warezak/PoundNineNewsWire/3DModel/Solidworks files/93365A11021-08-2015.SLDPRT

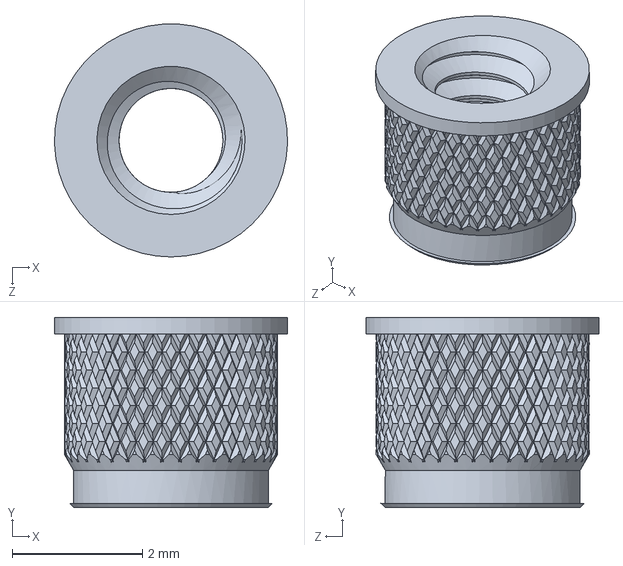
[picture p17: CAD file, 2016-02-17]
3DModel/Solidworks files/93365A11021-08-2015.SLDPRT
3.58 x 2.92 x 3.58 mm
