warezak/PoundNineNewsWire/XMegaFirmware/ATXMEGA_BASECODE/src/config/conf_sysfont.h

/**
 * \file
 *
 * \brief Default configurations for sysfont
 *
 * Copyright (c) 2012 Atmel Corporation. All rights reserved.
 *
 * \asf_license_start
 *
 * \page License
 *
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
 * 3. The name of Atmel may not be used to endorse or promote products derived
 *    from this software without specific prior written permission.
 *
 * 4. This software may only be redistributed and used in connection with an
 *    Atmel microcontroller product.
 *
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
 * \asf_license_stop
 *
 https://bitbucket.org/bperrybap/openglcd/src/86a2ff50f5da42badd289f6012b9200e9b2147bc/fonts/?at=master
 
 */
#ifndef CONF_SYSFONT_H
#define CONF_SYSFONT_H

/**
 * \weakgroup gfx_sysfont
 * @{
 */

#include <stdint.h>

 #define USE_FONT_BPMONO_10x16  // big font
/* #define USE_FONT_BPMONO_10x14 */
/* #define USE_FONT_MONO_MMM_10x12 */
#define USE_FONT_BASIC_6x7  // normal sys font


//#if defined(USE_FONT_BPMONO_10x16)
/** Width of each glyph, including spacer column. */
#  define BIGFONT_WIDTH           10
/** Height of each glyph, excluding spacer line. */
#  define BIGFONT_HEIGHT          16
/** Line height. */
#  define BIGFONT_LINESPACING     8
/** First character defined. */
#  define BIGFONT_FIRSTCHAR       ((uint8_t)' ')
/** Last character defined. */
#  define BIGFONT_LASTCHAR        ((uint8_t)'}')

/** Define variable containing the font */
#  define BIGFONT_DEFINE_GLYPHS \
        /* Glyph data, row by row, MSB is leftmost pixel, one byte per row. */ \
	static PROGMEM_DECLARE(uint8_t, bigfont_glyphs[]) = { \
		/* "BPmono" font (http://www.backpacker.gr) at size 10x16 */ \
		0x00, 0x00, 0x00, 0x00, 0x00, 0x00, 0x00, 0x00, 0x00, 0x00, \
		0x00, 0x00, 0x00, 0x00, 0x00, 0x00, 0x00, 0x00, 0x00, 0x00, \
		0x00, 0x00, 0x00, 0x00, 0x00, 0x00, 0x00, 0x00, 0x00, 0x00, \
		0x00, 0x00, /*   */ \
		0x00, 0x00, 0x00, 0x00, 0x00, 0x00, 0x30, 0x00, 0x30, 0x00, \
		0x30, 0x00, 0x30, 0x00, 0x30, 0x00, 0x30, 0x00, 0x30, 0x00, \
		0x00, 0x00, 0x30, 0x00, 0x30, 0x00, 0x00, 0x00, 0x00, 0x00, \
		0x00, 0x00, /* ! */ \
		0x00, 0x00, 0x00, 0x00, 0x00, 0x00, 0x6C, 0x00, 0x6C, 0x00, \
		0x6C, 0x00, 0x6C, 0x00, 0x00, 0x00, 0x00, 0x00, 0x00, 0x00, \
		0x00, 0x00, 0x00, 0x00, 0x00, 0x00, 0x00, 0x00, 0x00, 0x00, \
		0x00, 0x00, /* " */ \
		0x00, 0x00, 0x00, 0x00, 0x00, 0x00, 0x00, 0x00, 0x48, 0x00, \
		0x48, 0x00, 0xFC, 0x00, 0x48, 0x00, 0x48, 0x00, 0x48, 0x00, \
		0xFC, 0x00, 0x48, 0x00, 0x48, 0x00, 0x00, 0x00, 0x00, 0x00, \
		0x00, 0x00, /* # */ \
		0x00, 0x00, 0x00, 0x00, 0x00, 0x00, 0x10, 0x00, 0x10, 0x00, \
		0x3C, 0x00, 0x40, 0x00, 0x30, 0x00, 0x08, 0x00, 0x04, 0x00, \
		0x78, 0x00, 0x10, 0x00, 0x10, 0x00, 0x00, 0x00, 0x00, 0x00, \
		0x00, 0x00, /* $ */ \
		0x00, 0x00, 0x00, 0x00, 0x00, 0x00, 0x00, 0x00, 0x7C, 0x00, \
		0xA4, 0x00, 0xA8, 0x00, 0x48, 0x00, 0x10, 0x00, 0x14, 0x00, \
		0x2A, 0x00, 0x4A, 0x00, 0x44, 0x00, 0x00, 0x00, 0x00, 0x00, \
		0x00, 0x00, /* % */ \
		0x00, 0x00, 0x00, 0x00, 0x00, 0x00, 0x70, 0x00, 0x88, 0x00, \
		0x88, 0x00, 0x88, 0x00, 0x70, 0x00, 0x88, 0x00, 0x8A, 0x00, \
		0x8A, 0x00, 0x8C, 0x00, 0x70, 0x00, 0x00, 0x00, 0x00, 0x00, \
		0x00, 0x00, /* & */ \
		0x00, 0x00, 0x00, 0x00, 0x00, 0x00, 0x10, 0x00, 0x10, 0x00, \
		0x10, 0x00, 0x00, 0x00, 0x00, 0x00, 0x00, 0x00, 0x00, 0x00, \
		0x00, 0x00, 0x00, 0x00, 0x00, 0x00, 0x00, 0x00, 0x00, 0x00, \
		0x00, 0x00, /* ' */ \
		0x00, 0x00, 0x00, 0x00, 0x08, 0x00, 0x10, 0x00, 0x10, 0x00, \
		0x20, 0x00, 0x20, 0x00, 0x20, 0x00, 0x20, 0x00, 0x20, 0x00, \
		0x20, 0x00, 0x10, 0x00, 0x10, 0x00, 0x08, 0x00, 0x00, 0x00, \
		0x00, 0x00, /* ( */ \
		0x00, 0x00, 0x00, 0x00, 0x20, 0x00, 0x10, 0x00, 0x10, 0x00, \
		0x08, 0x00, 0x08, 0x00, 0x08, 0x00, 0x08, 0x00, 0x08, 0x00, \
		0x08, 0x00, 0x10, 0x00, 0x10, 0x00, 0x20, 0x00, 0x00, 0x00, \
		0x00, 0x00, /* ) */ \
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
	};

#if defined(USE_FONT_BPMONO_10x14)
/** Width of each glyph, including spacer column. */
#  define SYSFONT_WIDTH           10
/** Height of each glyph, excluding spacer line. */
#  define SYSFONT_HEIGHT          14
/** Line height. */
#  define SYSFONT_LINESPACING     8
/** First character defined. */
#  define SYSFONT_FIRSTCHAR       ((uint8_t)' ')
/** Last character defined. */
#  define SYSFONT_LASTCHAR        ((uint8_t)'}')

/** Define variable containing the font */
#  define SYSFONT_DEFINE_GLYPHS \
        /* Glyph data, row by row, MSB is leftmost pixel, one byte per row. */ \
	static PROGMEM_DECLARE(uint8_t, sysfont_glyphs[]) = { \
		/* "BPmono" font (http://www.backpacker.gr) at size 10x14 */ \
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
0x00,0x00,0x00,0x00,0x07,0x88,0x0F,0xF8,0x08,0xF0,0x00,0x00,0x00,0x00,0x00,0x00,0x00,0x00,0x00,0x00,0x00,0x00,0x00,0x00,0x00,0x00,0x00,0x00,0x00,0x00,0x00,0x00,  /* ~			*/\
};







///////////////////////////////////hack new
/////
//////** Width of each glyph, including spacer column. */
/////#  define HACK_FONT_WIDTH           8
//////** Height of each glyph, excluding spacer line. */
/////#  define HACK_FONT_HEIGHT          12
//////** Line height. */
/////#  define HACK_FONT_LINESPACING     8
//////** First character defined. */
/////#  define HACK_FONT_FIRSTCHAR       ((uint8_t)' ')
//////** Last character defined. */
/////#  define HACK_FONT_LASTCHAR        ((uint8_t)'}')
/////
//////** Define variable containing the font */
//////* Glyph data, row by row, MSB is leftmost pixel, one byte per row. */
/////
/////// 0x10,0x10,0x20,0x5F,
/////
///////Font Generated by MikroElektronika GLCD Font Creator 1.2.0.0
///////MikroElektronika 2011
///////http://www.mikroe.com
/////
///////GLCD FontName : Hack8x12
///////GLCD FontSize : 8 x 12
/////
/////#  define HACK_FONT_DEFINE_GLYPHS \
/////static PROGMEM_DECLARE(uint8_t, hack_font_glyphs[]) = { \
/////	0x05, 0x00, 0x00, 0x00, 0x00, 0x00, 0x00, 0x00, 0x00, 0x00, 0x00, 0x00, 0x00, 0x00, 0x00, 0x00, 0x00,  /* Code for char    	   */ \
/////	0x04, 0x00, 0x00, 0x00, 0x00, 0x00, 0x00, 0xBF, 0x01, 0x00, 0x00, 0x00, 0x00, 0x00, 0x00, 0x00, 0x00,  /* Code for char !	   */ \
/////	0x05, 0x00, 0x00, 0x00, 0x00, 0x07, 0x00, 0x00, 0x00, 0x07, 0x00, 0x00, 0x00, 0x00, 0x00, 0x00, 0x00,  /* Code for char "	   */ \
/////	0x07, 0x40, 0x00, 0xC8, 0x01, 0x78, 0x00, 0x4E, 0x01, 0xF8, 0x00, 0x4E, 0x00, 0x48, 0x00, 0x00, 0x00,  /* Code for char #	   */ \
/////	0x06, 0x00, 0x00, 0x9C, 0x01, 0x12, 0x01, 0xFF, 0x07, 0x22, 0x01, 0xE6, 0x00, 0x00, 0x00, 0x00, 0x00,  /* Code for char $	   */ \
/////	0x07, 0x4E, 0x00, 0x2A, 0x00, 0x2A, 0x00, 0xD4, 0x00, 0x30, 0x01, 0x30, 0x01, 0xC8, 0x00, 0x00, 0x00,  /* Code for char %	   */ \
/////	0x07, 0xF0, 0x00, 0x16, 0x01, 0x19, 0x01, 0x21, 0x01, 0xC1, 0x01, 0x80, 0x01, 0x60, 0x01, 0x00, 0x00,  /* Code for char &	   */ \
/////	0x04, 0x00, 0x00, 0x00, 0x00, 0x00, 0x00, 0x07, 0x00, 0x00, 0x00, 0x00, 0x00, 0x00, 0x00, 0x00, 0x00,  /* Code for char '	   */ \
/////	0x04, 0x00, 0x00, 0x00, 0x00, 0xFC, 0x01, 0x03, 0x06, 0x00, 0x00, 0x00, 0x00, 0x00, 0x00, 0x00, 0x00,  /* Code for char (	   */ \
/////	0x05, 0x00, 0x00, 0x00, 0x00, 0x00, 0x00, 0x03, 0x06, 0xFC, 0x01, 0x00, 0x00, 0x00, 0x00, 0x00, 0x00,  /* Code for char )	   */ \
/////	0x06, 0x00, 0x00, 0x24, 0x00, 0x14, 0x00, 0x0F, 0x00, 0x14, 0x00, 0x24, 0x00, 0x00, 0x00, 0x00, 0x00,  /* Code for char *	   */ \
/////	0x07, 0x20, 0x00, 0x20, 0x00, 0x20, 0x00, 0xFC, 0x01, 0x20, 0x00, 0x20, 0x00, 0x20, 0x00, 0x00, 0x00,  /* Code for char +	   */ \
/////	0x05, 0x00, 0x00, 0x00, 0x00, 0x00, 0x00, 0x80, 0x05, 0x80, 0x03, 0x00, 0x00, 0x00, 0x00, 0x00, 0x00,  /* Code for char ,	   */ \
/////	0x06, 0x00, 0x00, 0x20, 0x00, 0x20, 0x00, 0x20, 0x00, 0x20, 0x00, 0x20, 0x00, 0x00, 0x00, 0x00, 0x00,  /* Code for char -	   */ \
/////	0x04, 0x00, 0x00, 0x00, 0x00, 0x00, 0x00, 0x00, 0x01, 0x00, 0x00, 0x00, 0x00, 0x00, 0x00, 0x00, 0x00,  /* Code for char .	   */ \
/////	0x06, 0x00, 0x02, 0x80, 0x01, 0x60, 0x00, 0x18, 0x00, 0x06, 0x00, 0x01, 0x00, 0x00, 0x00, 0x00, 0x00,  /* Code for char /	   */ \
/////	0x06, 0x7C, 0x00, 0xFF, 0x01, 0x01, 0x01, 0x39, 0x01, 0x83, 0x00, 0x7C, 0x00, 0x00, 0x00, 0x00, 0x00,  /* Code for char 0	   */ \
/////	0x07, 0x00, 0x00, 0x00, 0x00, 0x02, 0x01, 0x01, 0x01, 0xFF, 0x01, 0x00, 0x01, 0x00, 0x01, 0x00, 0x00,  /* Code for char 1	   */ \
/////	0x06, 0x00, 0x00, 0x03, 0x01, 0xC1, 0x01, 0x21, 0x01, 0x11, 0x01, 0x0E, 0x01, 0x00, 0x00, 0x00, 0x00,  /* Code for char 2	   */ \
/////	0x06, 0x00, 0x00, 0x81, 0x01, 0x01, 0x01, 0x11, 0x01, 0x11, 0x01, 0xEE, 0x00, 0x00, 0x00, 0x00, 0x00,  /* Code for char 3	   */ \
/////	0x06, 0x60, 0x00, 0x70, 0x00, 0x4C, 0x00, 0x42, 0x00, 0xFF, 0x01, 0x40, 0x00, 0x00, 0x00, 0x00, 0x00,  /* Code for char 4	   */ \
/////	0x06, 0x00, 0x00, 0x8F, 0x01, 0x09, 0x01, 0x09, 0x01, 0x09, 0x01, 0xF0, 0x00, 0x00, 0x00, 0x00, 0x00,  /* Code for char 5	   */ \
/////	0x06, 0x00, 0x00, 0xFC, 0x00, 0x9B, 0x01, 0x09, 0x01, 0x09, 0x01, 0xF1, 0x00, 0x00, 0x00, 0x00, 0x00,  /* Code for char 6	   */ \
/////	0x07, 0x00, 0x00, 0x01, 0x00, 0x01, 0x01, 0xC1, 0x01, 0x71, 0x00, 0x0F, 0x00, 0x03, 0x00, 0x00, 0x00,  /* Code for char 7	   */ \
/////	0x06, 0x00, 0x00, 0xEE, 0x00, 0x11, 0x01, 0x11, 0x01, 0x11, 0x01, 0xEE, 0x00, 0x00, 0x00, 0x00, 0x00,  /* Code for char 8	   */ \
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
	  0x3F,0xF8,  0x20,0x08,  0x20,0x08,  0x3F,0xF8,  0x00,0x00,  0x00,0x00,  0x00,0x00,  0x00,0x00,  0x00,0x00   /* Code for char   */ \
};
#endif /* CONF_SYSFONT_H */
