warezak/PoundNineNewsWire/XMegaFirmware/ATXMEGA_BASECODE/project_lib/Adafruit_CC3100/simplelink/include/socket.h

/*
 * socket.h - CC31xx/CC32xx Host Driver Implementation
 *
 * Copyright (C) 2014 Texas Instruments Incorporated - http://www.ti.com/ 
 * 
 * 
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
 *    Redistributions of source code must retain the above copyright 
 *    notice, this list of conditions and the following disclaimer.
 *
 *    Redistributions in binary form must reproduce the above copyright
 *    notice, this list of conditions and the following disclaimer in the 
 *    documentation and/or other materials provided with the   
 *    distribution.
 *
 *    Neither the name of Texas Instruments Incorporated nor the names of
 *    its contributors may be used to endorse or promote products derived
 *    from this software without specific prior written permission.
 *
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
*/
 
/*****************************************************************************/
/* Include files                                                             */
/*****************************************************************************/
#include "simplelink.h"

#ifndef __SL_SOCKET_H__
#define __SL_SOCKET_H__




#ifdef    __cplusplus
extern "C" {
#endif

/*!

    \addtogroup socket
    @{

*/

/*****************************************************************************/
/* Macro declarations                                                        */
/*****************************************************************************/

#define SL_FD_SETSIZE                         SL_MAX_SOCKETS         /* Number of sockets to select on - same is max sockets!               */
#define BSD_SOCKET_ID_MASK                     (0x0F)                 /* Index using the LBS 4 bits for socket id 0-7 */
/* Define some BSD protocol constants.  */
#define SL_SOCK_STREAM                         (1)                       /* TCP Socket                                                          */
#define SL_SOCK_DGRAM                          (2)                       /* UDP Socket                                                          */
#define SL_SOCK_RAW                            (3)                       /* Raw socket                                                          */
#define SL_IPPROTO_TCP                         (6)                       /* TCP Raw Socket                                                      */
#define SL_IPPROTO_UDP                         (17)                      /* UDP Raw Socket                                                      */
#define SL_IPPROTO_RAW                         (255)                     /* Raw Socket                                                          */
#define SL_SEC_SOCKET                          (100)                     /* Secured Socket Layer (SSL,TLS)                                      */

/* Address families.  */
#define     SL_AF_INET                         (2)                       /* IPv4 socket (UDP, TCP, etc)                                          */
#define     SL_AF_INET6                        (3)                       /* IPv6 socket (UDP, TCP, etc)                                          */
#define     SL_AF_INET6_EUI_48                 (9)
#define     SL_AF_RF                           (6)                       /* data include RF parameter, All layer by user (Wifi could be disconnected) */ 
#define     SL_AF_PACKET                       (17)
/* Protocol families, same as address families.  */
#define     SL_PF_INET                         AF_INET
#define     SL_PF_INET6                        AF_INET6
#define     SL_INADDR_ANY                      (0)                       /*  bind any address  */

/* error codes */
#define SL_SOC_ERROR                          (-1)  /* Failure.                                                             */
#define SL_SOC_OK                             ( 0)  /* Success.                                                             */
#define SL_INEXE                              (-8)   /* socket command in execution  */
#define SL_EBADF                              (-9)   /* Bad file number */
#define SL_ENSOCK                             (-10)  /* The system limit on the total number of open socket, has been reached */
#define SL_EAGAIN                             (-11)  /* Try again */
#define SL_EWOULDBLOCK                        SL_EAGAIN
#define SL_ENOMEM                             (-12)  /* Out of memory */
#define SL_EACCES                             (-13)  /* Permission denied */
#define SL_EFAULT                             (-14)  /* Bad address */
#define SL_ECLOSE                             (-15)  /* close socket operation failed to transmit all queued packets */
#define SL_EALREADY_ENABLED                   (-21)  /* Transceiver - Transceiver already ON. there could be only one */
#define SL_EINVAL                             (-22)  /* Invalid argument */
#define SL_EAUTO_CONNECT_OR_CONNECTING        (-69)  /* Transceiver - During connection, connected or auto mode started */
#define SL_CONNECTION_PENDING                  (-72)  /* Transceiver - Device is connected, disconnect first to open transceiver */
#define SL_EUNSUPPORTED_ROLE                  (-86)  /* Transceiver - Trying to start when WLAN role is AP or P2P GO */
#define SL_EDESTADDRREQ                       (-89)  /* Destination address required */
#define SL_EPROTOTYPE                         (-91)  /* Protocol wrong type for socket */
#define SL_ENOPROTOOPT                        (-92)  /* Protocol not available */
#define SL_EPROTONOSUPPORT                    (-93)  /* Protocol not supported */
#define SL_ESOCKTNOSUPPORT                    (-94)  /* Socket type not supported */
#define SL_EOPNOTSUPP                         (-95)  /* Operation not supported on transport endpoint */
#define SL_EAFNOSUPPORT                       (-97)  /* Address family not supported by protocol */
#define SL_EADDRINUSE                         (-98)  /* Address already in use */
#define SL_EADDRNOTAVAIL                      (-99)  /* Cannot assign requested address */
#define SL_ENETUNREACH                        (-101) /* Network is unreachable */
#define SL_ENOBUFS                            (-105) /* No buffer space available */
#define SL_EOBUFF                             SL_ENOBUFS 
#define SL_EISCONN                            (-106) /* Transport endpoint is already connected */
#define SL_ENOTCONN                           (-107) /* Transport endpoint is not connected */
#define SL_ETIMEDOUT                          (-110) /* Connection timed out */
#define SL_ECONNREFUSED                       (-111) /* Connection refused */
#define SL_EALREADY                           (-114) /* Non blocking connect in progress, try again */ 

#define SL_ESEC_RSA_WRONG_TYPE_E              (-130)  /* RSA wrong block type for RSA function */
#define SL_ESEC_RSA_BUFFER_E                  (-131)  /* RSA buffer error, output too small or */
#define SL_ESEC_BUFFER_E                      (-132)  /* output buffer too small or input too large */
#define SL_ESEC_ALGO_ID_E                     (-133)  /* setting algo id error */
#define SL_ESEC_PUBLIC_KEY_E                  (-134)  /* setting public key error */
#define SL_ESEC_DATE_E                        (-135)  /* setting date validity error */
#define SL_ESEC_SUBJECT_E                     (-136)  /* setting subject name error */
#define SL_ESEC_ISSUER_E                      (-137)  /* setting issuer  name error */
#define SL_ESEC_CA_TRUE_E                     (-138)  /* setting CA basic constraint true error */
#define SL_ESEC_EXTENSIONS_E                  (-139)  /* setting extensions error */
#define SL_ESEC_ASN_PARSE_E                   (-140)  /* ASN parsing error, invalid input */
#define SL_ESEC_ASN_VERSION_E                 (-141)  /* ASN version error, invalid number */
#define SL_ESEC_ASN_GETINT_E                  (-142)  /* ASN get big _i16 error, invalid data */
#define SL_ESEC_ASN_RSA_KEY_E                 (-143)  /* ASN key init error, invalid input */
#define SL_ESEC_ASN_OBJECT_ID_E               (-144)  /* ASN object id error, invalid id */
#define SL_ESEC_ASN_TAG_NULL_E                (-145)  /* ASN tag error, not null */
#define SL_ESEC_ASN_EXPECT_0_E                (-146)  /* ASN expect error, not zero */
#define SL_ESEC_ASN_BITSTR_E                  (-147)  /* ASN bit string error, wrong id */
#define SL_ESEC_ASN_UNKNOWN_OID_E             (-148)  /* ASN oid error, unknown sum id */
#define SL_ESEC_ASN_DATE_SZ_E                 (-149)  /* ASN date error, bad size */
#define SL_ESEC_ASN_BEFORE_DATE_E             (-150)  /* ASN date error, current date before */
#define SL_ESEC_ASN_AFTER_DATE_E              (-151)  /* ASN date error, current date after */
#define SL_ESEC_ASN_SIG_OID_E                 (-152)  /* ASN signature error, mismatched oid */
#define SL_ESEC_ASN_TIME_E                    (-153)  /* ASN time error, unknown time type */
#define SL_ESEC_ASN_INPUT_E                   (-154)  /* ASN input error, not enough data */
#define SL_ESEC_ASN_SIG_CONFIRM_E             (-155)  /* ASN sig error, confirm failure */
#define SL_ESEC_ASN_SIG_HASH_E                (-156)  /* ASN sig error, unsupported hash type */
#define SL_ESEC_ASN_SIG_KEY_E                 (-157)  /* ASN sig error, unsupported key type */
#define SL_ESEC_ASN_DH_KEY_E                  (-158)  /* ASN key init error, invalid input */
#define SL_ESEC_ASN_NTRU_KEY_E                (-159)  /* ASN ntru key decode error, invalid input */
#define SL_ESEC_ECC_BAD_ARG_E                 (-170)  /* ECC input argument of wrong type */
#define SL_ESEC_ASN_ECC_KEY_E                 (-171)  /* ASN ECC bad input */
#define SL_ESEC_ECC_CURVE_OID_E               (-172)  /* Unsupported ECC OID curve type */
#define SL_ESEC_BAD_FUNC_ARG                  (-173)  /* Bad function argument provided */
#define SL_ESEC_NOT_COMPILED_IN               (-174)  /* Feature not compiled in */
#define SL_ESEC_UNICODE_SIZE_E                (-175)  /* Unicode password too big */
#define SL_ESEC_NO_PASSWORD                   (-176)  /* no password provided by user */
#define SL_ESEC_ALT_NAME_E                    (-177)  /* alt name size problem, too big */
#define SL_ESEC_AES_GCM_AUTH_E                (-180)  /* AES-GCM Authentication check failure */
#define SL_ESEC_AES_CCM_AUTH_E                (-181)  /* AES-CCM Authentication check failure */
#define SL_SOCKET_ERROR_E                     (-208)  /* Error state on socket */

#define SL_ESEC_MEMORY_ERROR                  (-203)  /* out of memory            */
#define SL_ESEC_VERIFY_FINISHED_ERROR         (-204)  /* verify problem on finished */
#define SL_ESEC_VERIFY_MAC_ERROR              (-205)  /* verify mac problem       */
#define SL_ESEC_UNKNOWN_HANDSHAKE_TYPE        (-207)  /* weird handshake type     */
#define SL_ESEC_SOCKET_ERROR_E                (-208)  /* error state on socket    */
#define SL_ESEC_SOCKET_NODATA                 (-209)  /* expected data, not there */
#define SL_ESEC_INCOMPLETE_DATA               (-210)  /* don't have enough data to complete task            */
#define SL_ESEC_UNKNOWN_RECORD_TYPE           (-211)  /* unknown type in record hdr */
#define SL_ESEC_FATAL_ERROR                   (-213)  /* recvd alert fatal error  */
#define SL_ESEC_ENCRYPT_ERROR                 (-214)  /* error during encryption  */
#define SL_ESEC_NO_PEER_KEY                   (-216)  /* need peer's key          */
#define SL_ESEC_NO_PRIVATE_KEY                (-217)  /* need the private key     */
#define SL_ESEC_RSA_PRIVATE_ERROR             (-218)  /* error during rsa priv op */
#define SL_ESEC_NO_DH_PARAMS                  (-219)  /* server missing DH params */
#define SL_ESEC_BUILD_MSG_ERROR               (-220)  /* build message failure    */
#define SL_ESEC_BAD_HELLO                     (-221)  /* client hello malformed   */
#define SL_ESEC_DOMAIN_NAME_MISMATCH          (-222)  /* peer subject name mismatch */
#define SL_ESEC_WANT_READ                     (-223)  /* want read, call again    */
#define SL_ESEC_NOT_READY_ERROR               (-224)  /* handshake layer not ready */
#define SL_ESEC_PMS_VERSION_ERROR             (-225)  /* pre m secret version error */
#define SL_ESEC_VERSION_ERROR                 (-226)  /* record layer version error */
#define SL_ESEC_WANT_WRITE                    (-227)  /* want write, call again   */
#define SL_ESEC_BUFFER_ERROR                  (-228)  /* malformed buffer input   */
#define SL_ESEC_VERIFY_CERT_ERROR             (-229)  /* verify cert error        */
#define SL_ESEC_VERIFY_SIGN_ERROR             (-230)  /* verify sign error        */

#define SL_ESEC_LENGTH_ERROR                  (-241)  /* record layer length error */
#define SL_ESEC_PEER_KEY_ERROR                (-242)  /* can't decode peer key */
#define SL_ESEC_ZERO_RETURN                   (-243)  /* peer sent close notify */
#define SL_ESEC_SIDE_ERROR                    (-244)  /* wrong client/server type */
#define SL_ESEC_NO_PEER_CERT                  (-245)  /* peer didn't send key */
#define SL_ESEC_ECC_CURVETYPE_ERROR           (-250)  /* Bad ECC Curve Type */
#define SL_ESEC_ECC_CURVE_ERROR               (-251)  /* Bad ECC Curve */
#define SL_ESEC_ECC_PEERKEY_ERROR             (-252)  /* Bad Peer ECC Key */
#define SL_ESEC_ECC_MAKEKEY_ERROR             (-253)  /* Bad Make ECC Key */
#define SL_ESEC_ECC_EXPORT_ERROR              (-254)  /* Bad ECC Export Key */
#define SL_ESEC_ECC_SHARED_ERROR              (-255)  /* Bad ECC Shared Secret */
#define SL_ESEC_NOT_CA_ERROR                  (-257)  /* Not a CA cert error */
#define SL_ESEC_BAD_PATH_ERROR                (-258)  /* Bad path for opendir */
#define SL_ESEC_BAD_CERT_MANAGER_ERROR        (-259)  /* Bad Cert Manager */
#define SL_ESEC_MAX_CHAIN_ERROR               (-268)  /* max chain depth exceeded */
#define SL_ESEC_SUITES_ERROR                  (-271)  /* suites pointer error */
#define SL_ESEC_SSL_NO_PEM_HEADER             (-272)  /* no PEM header found */
#define SL_ESEC_OUT_OF_ORDER_E                (-273)  /* out of order message */
#define SL_ESEC_SANITY_CIPHER_E               (-275)  /* sanity check on cipher error */
#define SL_ESEC_GEN_COOKIE_E                  (-277)  /* Generate Cookie Error */
#define SL_ESEC_NO_PEER_VERIFY                (-278)  /* Need peer cert verify Error */
#define SL_ESEC_UNKNOWN_SNI_HOST_NAME_E       (-281)  /* Unrecognized host name Error */
/* begin negotiation parameter errors */
#define SL_ESEC_UNSUPPORTED_SUITE     (-290)            /* unsupported cipher suite */
#define SL_ESEC_MATCH_SUITE_ERROR      (-291 )            /* can't match cipher suite */

/* ssl tls security start with -300 offset */
#define SL_ESEC_CLOSE_NOTIFY                  (-300) /* ssl/tls alerts */   
#define SL_ESEC_UNEXPECTED_MESSAGE            (-310) /* ssl/tls alerts */   
#define SL_ESEC_BAD_RECORD_MAC                (-320) /* ssl/tls alerts */                 
#define SL_ESEC_DECRYPTION_FAILED             (-321) /* ssl/tls alerts */   
#define SL_ESEC_RECORD_OVERFLOW               (-322) /* ssl/tls alerts */    
#define SL_ESEC_DECOMPRESSION_FAILURE         (-330) /* ssl/tls alerts */                 
#define SL_ESEC_HANDSHAKE_FAILURE             (-340) /* ssl/tls alerts */    
#define SL_ESEC_NO_CERTIFICATE                (-341) /* ssl/tls alerts */    
#define SL_ESEC_BAD_CERTIFICATE               (-342) /* ssl/tls alerts */          
#define SL_ESEC_UNSUPPORTED_CERTIFICATE       (-343) /* ssl/tls alerts */     
#define SL_ESEC_CERTIFICATE_REVOKED           (-344) /* ssl/tls alerts */                 
#define SL_ESEC_CERTIFICATE_EXPIRED           (-345) /* ssl/tls alerts */                 
#define SL_ESEC_CERTIFICATE_UNKNOWN           (-346) /* ssl/tls alerts */                 
#define SL_ESEC_ILLEGAL_PARAMETER             (-347) /* ssl/tls alerts */                 
#define SL_ESEC_UNKNOWN_CA                    (-348) /* ssl/tls alerts */                
#define SL_ESEC_ACCESS_DENIED                 (-349) /* ssl/tls alerts */                
#define SL_ESEC_DECODE_ERROR                  (-350) /* ssl/tls alerts */   
#define SL_ESEC_DECRYPT_ERROR                 (-351) /* ssl/tls alerts */   
#define SL_ESEC_EXPORT_RESTRICTION            (-360) /* ssl/tls alerts */    
#define SL_ESEC_PROTOCOL_VERSION              (-370) /* ssl/tls alerts */    
#define SL_ESEC_INSUFFICIENT_SECURITY         (-371) /* ssl/tls alerts */   
#define SL_ESEC_INTERNAL_ERROR                (-380) /* ssl/tls alerts */   
#define SL_ESEC_USER_CANCELLED                (-390) /* ssl/tls alerts */   
#define SL_ESEC_NO_RENEGOTIATION              (-400) /* ssl/tls alerts */   
#define SL_ESEC_UNSUPPORTED_EXTENSION         (-410) /* ssl/tls alerts */   
#define SL_ESEC_CERTIFICATE_UNOBTAINABLE      (-411) /* ssl/tls alerts */         
#define SL_ESEC_UNRECOGNIZED_NAME             (-412) /* ssl/tls alerts */   
#define SL_ESEC_BAD_CERTIFICATE_STATUS_RESPONSE  (-413) /* ssl/tls alerts */   
#define SL_ESEC_BAD_CERTIFICATE_HASH_VALUE    (-414) /* ssl/tls alerts */   
/* propierty secure */
#define SL_ESECGENERAL                        (-450)  /* error secure level general error */
#define SL_ESECDECRYPT                        (-451)  /* error secure level, decrypt recv packet fail */
#define SL_ESECCLOSED                         (-452)  /* secure layrer is closed by other size , tcp is still connected  */
#define SL_ESECSNOVERIFY                      (-453)  /* Connected without server verification */
#define SL_ESECNOCAFILE                       (-454)  /* error secure level CA file not found*/
#define SL_ESECMEMORY                         (-455)  /* error secure level No memory  space available */
#define SL_ESECBADCAFILE                      (-456)  /* error secure level bad CA file */
#define SL_ESECBADCERTFILE                    (-457)  /* error secure level bad Certificate file */
#define SL_ESECBADPRIVATEFILE                 (-458)  /* error secure level bad private file */
#define SL_ESECBADDHFILE                      (-459)  /* error secure level bad DH file */
#define SL_ESECT00MANYSSLOPENED               (-460)  /* MAX SSL Sockets are opened */
#define SL_ESECDATEERROR                      (-461)  /* connected with certificate date verification error */
#define SL_ESECHANDSHAKETIMEDOUT              (-462)  /* connection timed out due to handshake time */

/* end error codes */

/* Max payload size by protocol */
#define SL_SOCKET_PAYLOAD_TYPE_MASK            (0xF0)  /*4 bits type, 4 bits sockets id */
#define SL_SOCKET_PAYLOAD_TYPE_UDP_IPV4        (0x00)  /* 1472 bytes */
#define SL_SOCKET_PAYLOAD_TYPE_TCP_IPV4        (0x10)  /* 1460 bytes */
#define SL_SOCKET_PAYLOAD_TYPE_UDP_IPV6        (0x20)  /* 1452 bytes */
#define SL_SOCKET_PAYLOAD_TYPE_TCP_IPV6        (0x30)  /* 1440 bytes */
#define SL_SOCKET_PAYLOAD_TYPE_UDP_IPV4_SECURE (0x40)  /*            */
#define SL_SOCKET_PAYLOAD_TYPE_TCP_IPV4_SECURE (0x50)  /*            */
#define SL_SOCKET_PAYLOAD_TYPE_UDP_IPV6_SECURE (0x60)  /*            */
#define SL_SOCKET_PAYLOAD_TYPE_TCP_IPV6_SECURE (0x70)  /*            */
#define SL_SOCKET_PAYLOAD_TYPE_RAW_TRANCEIVER  (0x80)  /* 1536 bytes */
#define SL_SOCKET_PAYLOAD_TYPE_RAW_PACKET      (0x90)  /* 1536 bytes */
#define SL_SOCKET_PAYLOAD_TYPE_RAW_IP4         (0xa0)  
#define SL_SOCKET_PAYLOAD_TYPE_RAW_IP6         (SL_SOCKET_PAYLOAD_TYPE_RAW_IP4 )  

  

#define SL_SOL_SOCKET          (1)   /* Define the socket option category. */
#define SL_IPPROTO_IP          (2)   /* Define the IP option category.     */
#define SL_SOL_PHY_OPT         (3)   /* Define the PHY option category.    */
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
